Abrechen2/AirQualityMonitor/Pictures/IMG_7562.JPEG

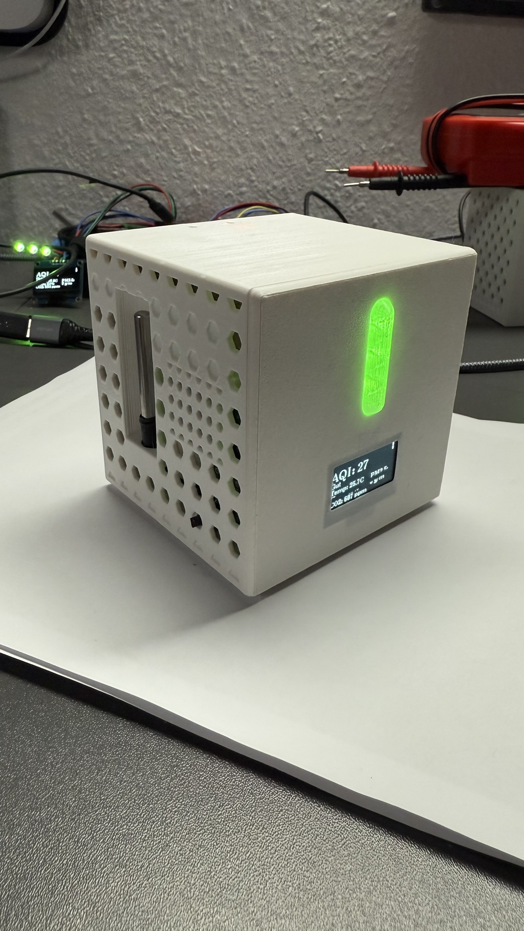
Pictures/IMG_7562.JPEG
