Abrechen2/AirQualityMonitor/Pictures/IMG_7563.JPEG

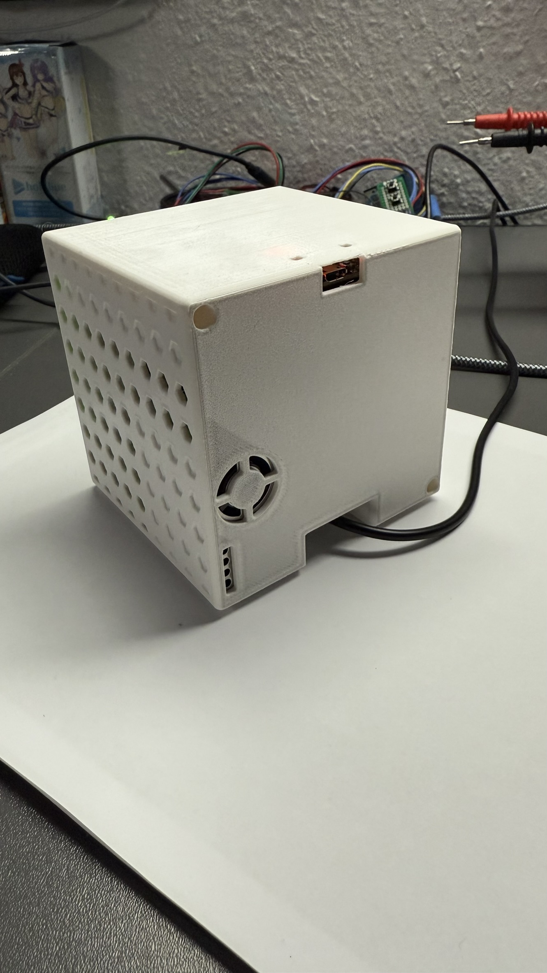
Pictures/IMG_7563.JPEG
