Abrechen2/AirQualityMonitor/Pictures/IMG_7564.JPEG

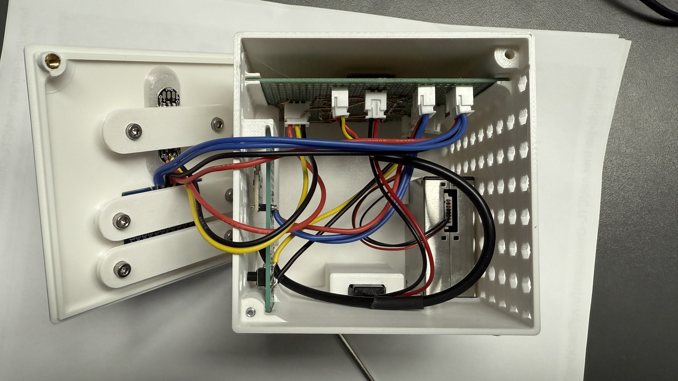
Pictures/IMG_7564.JPEG
