Abrechen2/AirQualityMonitor/Pictures/IMG_7565.JPEG

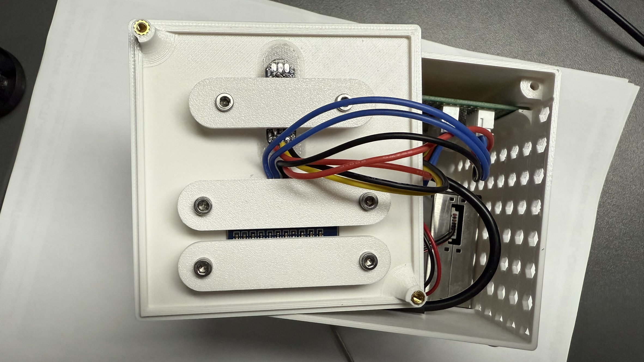
Pictures/IMG_7565.JPEG
