Abrechen2/AirQualityMonitor/Pictures/IMG_7566.JPEG

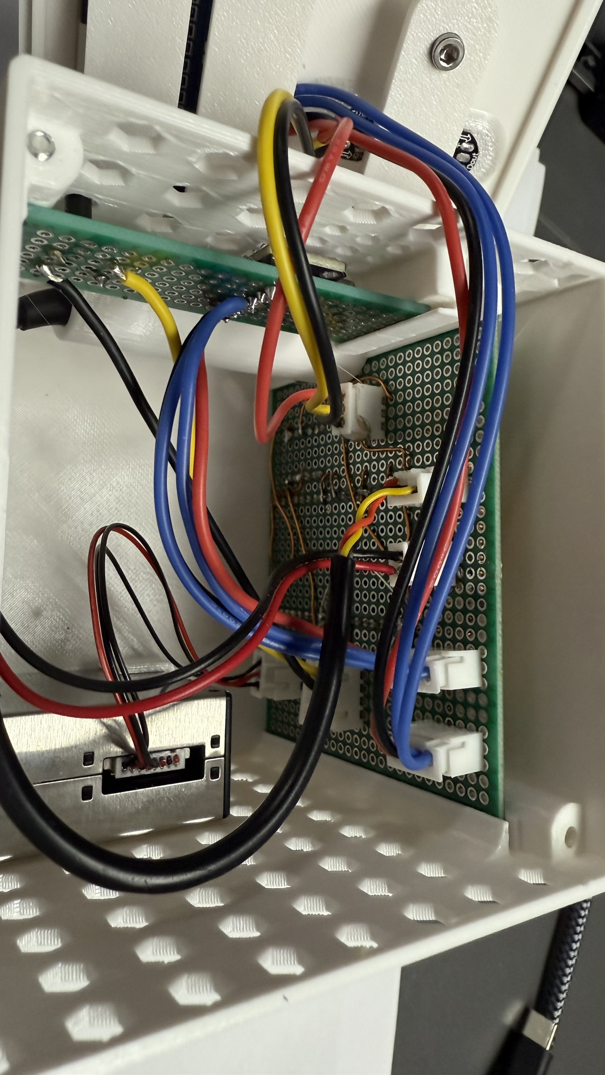
Pictures/IMG_7566.JPEG
