Abrechen2/AirQualityMonitor/Pictures/IMG_7568.JPEG

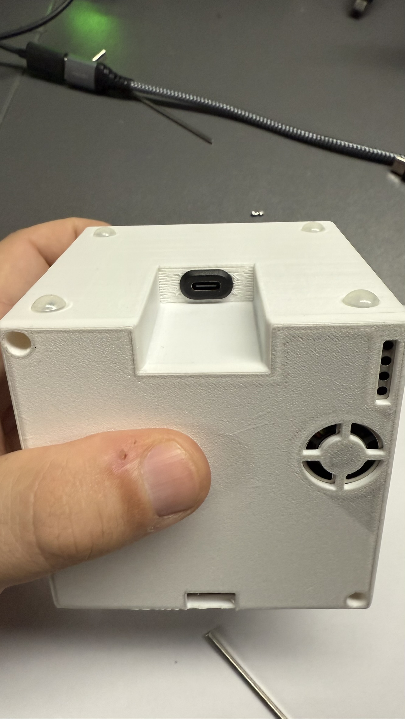
Pictures/IMG_7568.JPEG
