Abrechen2/AirQualityMonitor/Schematics/KiCad/AirQualityMonitor.kicad_sch

## KiCad design Schematics/KiCad/AirQualityMonitor.kicad_sch (2025-08-20, an earlier design)

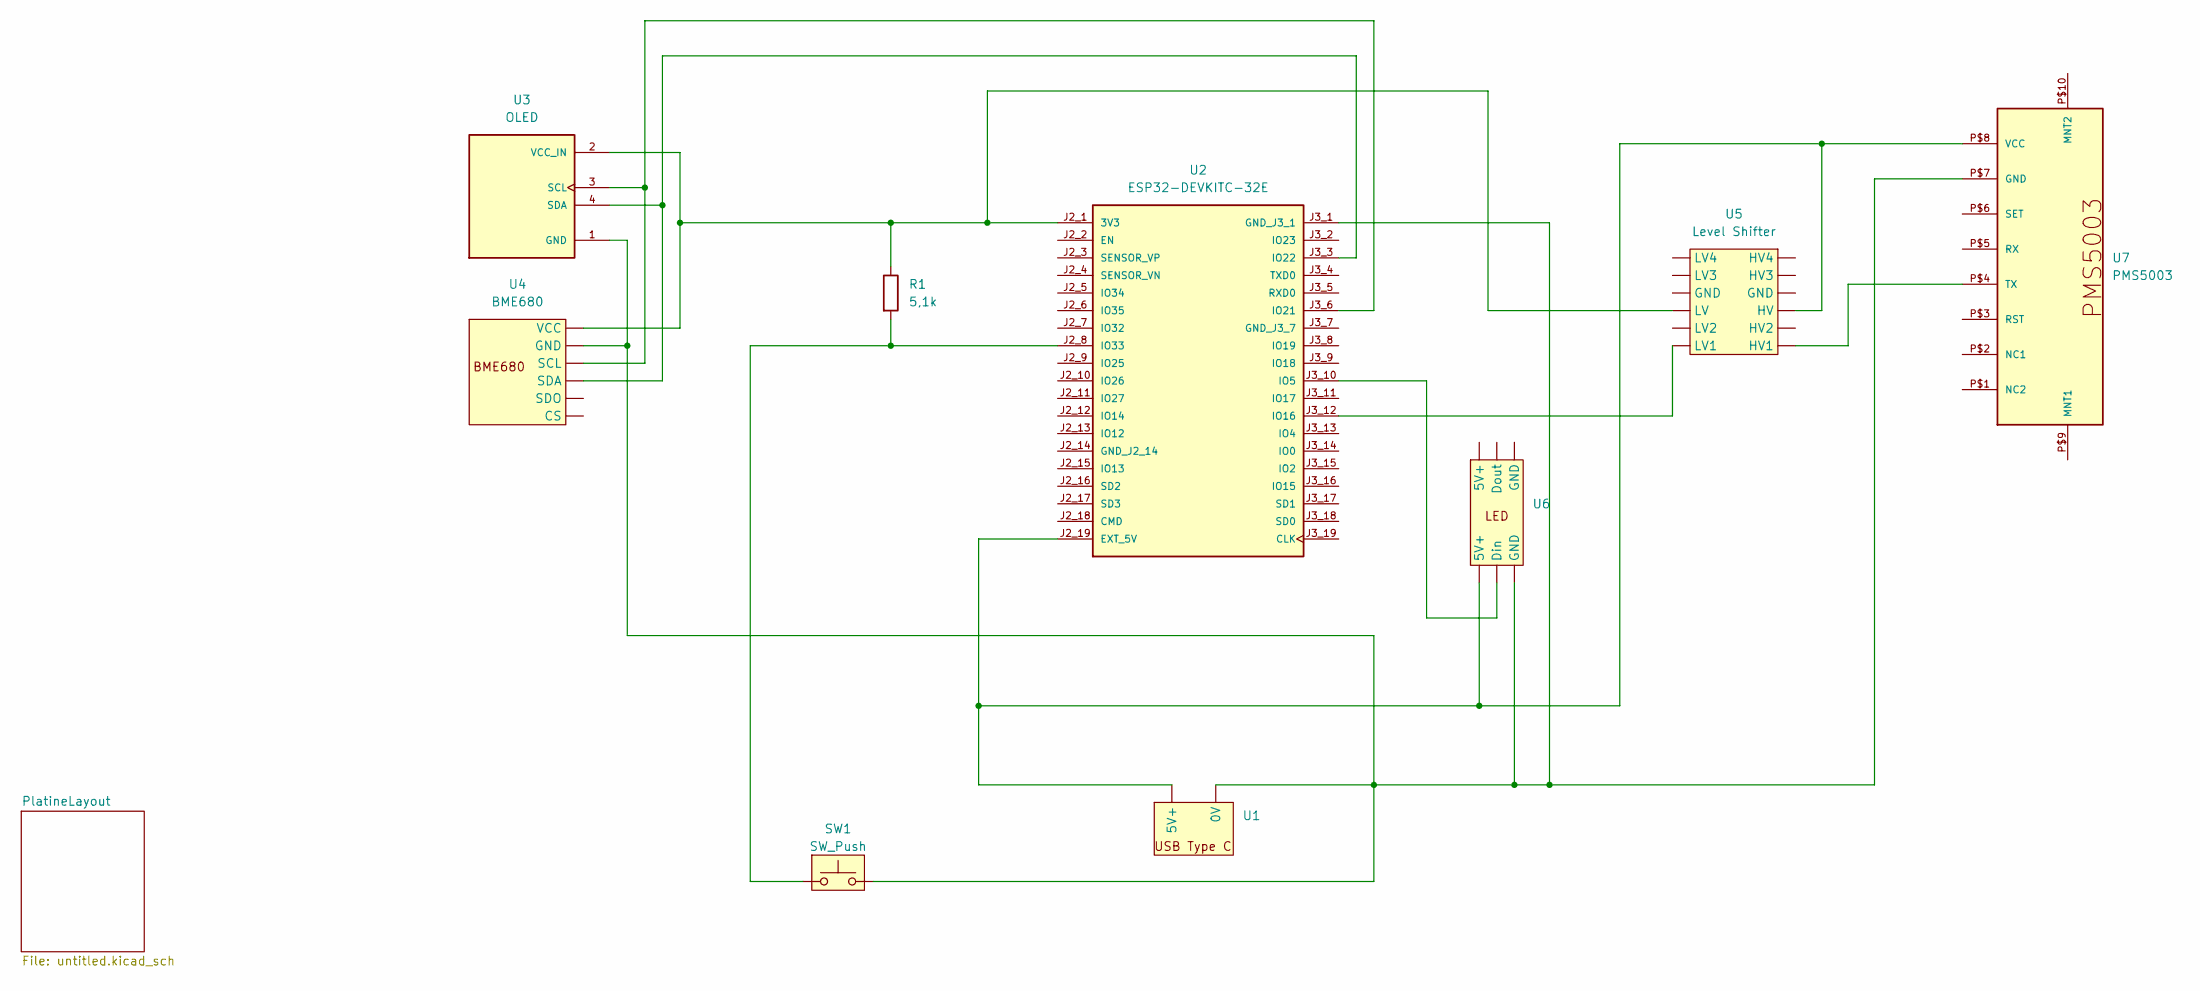
[picture p17: schematic AirQualityMonitor.kicad_sch]

Parts:
R1: 5,1k
SW1: SW_Push
U1, U6: (no value)
U2: ESP32-DEVKITC-32E; MODULE_ESP32-DEVKITC-32E; PARTREV 1.4
U3: OLED; MODULE_DM-OLED096-636; PARTREV 2018-09-10
U4: BME680
U5: Level Shifter
U7: PMS5003

Connections:
unnamed: R1.1, U2.J2_1 (3V3), U3.2 (VCC_IN), U4., U5.
unnamed: R1.2, SW1.1, U2.J2_8 (IO33)
unnamed: SW1.2, U1., U2.J3_1 (GND_J3_1), U3.1 (GND), U4., U6., U7.P$7 (GND)
unnamed: U1., U2.J2_19 (EXT_5V), U5., U6., U7.P$8 (VCC)
unnamed: U2.J3_3 (IO22), U3.4 (SDA), U4.
unnamed: U2.J3_6 (IO21), U3.3 (SCL), U4.
unnamed: U2.J3_10 (IO5), U6.
unnamed: U2.J3_12 (IO16), U5.
unnamed: U5., U7.P$4 (TX)
