Abrechen2/AirQualityMonitor/DisplayManager.h

#ifndef DISPLAY_MANAGER_H
#define DISPLAY_MANAGER_H

#include <Arduino.h>
#include <U8g2lib.h>
#include <Adafruit_NeoPixel.h>
#include <WiFi.h>
#include "config.h"
#include "SensorManager.h"
#include "TimeUtils.h"

// ===== DISPLAY MANAGER CLASS =====
class DisplayManager {
private:
  U8G2_SH1106_128X64_NONAME_F_HW_I2C& display;
  Adafruit_NeoPixel& leds;
  
  DisplayView currentView = VIEW_OVERVIEW;
  StealthMode stealthMode = STEALTH_OFF;
  bool displayEnabled = true;
  unsigned long stealthTempStartTime = 0;

  // Stealth countdown overlay state (driven by ButtonHandler during long press)
  bool countdownActive = false;
  int8_t lastDrawnCountdownSecond = -1;

  // Cache of last-drawn frame — lets us restore the normal view
  // immediately after the countdown overlay ends without waiting
  // for the next sensor update (~3s).
  SensorData lastSensorData{};
  float lastAqi = 0.0f;
  String lastAqiLevel = "";
  bool lastWifiConnected = false;
  bool hasLastFrame = false;

public:
  DisplayManager(U8G2_SH1106_128X64_NONAME_F_HW_I2C& disp, Adafruit_NeoPixel& strip);

  void init();
  void updateDisplay(const SensorData& data, float aqi, const String& aqiLevel,
                     bool wifiConnected);
  void showMessage(const String& message, int duration = 1000);

  // View control
  void nextView();
  void toggleStealth();
  void activateStealthTemp();

  // Stealth countdown overlay — called from ButtonHandler during long press
  void showStealthCountdown(uint16_t remainingMs);
  void hideStealthCountdown();
  bool isCountdownActive() const { return countdownActive; }

  // Status
  bool isDisplayEnabled() const { return displayEnabled; }
  DisplayView getCurrentView() const { return currentView; }
  StealthMode getStealthMode() const { return stealthMode; }

  void resetActivity() { /* no longer used */ }

private:
    void drawOverview(const SensorData& data, float aqi, const String& aqiLevel, bool wifiConnected);
    void drawEnvironment(const SensorData& data, bool wifiConnected);
    void drawParticles(const SensorData& data, float aqi, bool wifiConnected);
    void drawGas(const SensorData& data, bool wifiConnected);
    void drawSystem(const SensorData& data, bool wifiConnected);
    void drawWiFiIcon(int x, int y, bool connected);
    void drawConnectionBar(int x, int y, bool wifiConnected);
    String getShortLevelName(const String& level);
    // Helper for icon drawing - reduces duplication
    void drawStatusIcon(int x, int y, bool connected, bool isWiFi);
  void updateStealthMode();
  void updateDisplayBrightness();
  void drawStealthCountdownFrame(int seconds);
};

// ===== IMPLEMENTATION =====
DisplayManager::DisplayManager(U8G2_SH1106_128X64_NONAME_F_HW_I2C& disp, Adafruit_NeoPixel& strip) 
  : display(disp), leds(strip) {
}

void DisplayManager::init() {
  DEBUG_INFO("Initializing display...");
  
  // Check if display is available
  Wire.beginTransmission(0x3C);
  if (Wire.endTransmission() != 0) {
    DEBUG_WARN("Display not available");
    displayEnabled = false;
    return;
  }
  
  display.begin();
  display.clearBuffer();
  display.setFont(u8g2_font_ncenB08_tr);
  display.drawStr(10, 30, "Booting...");
  display.sendBuffer();
  
  updateDisplayBrightness();
  
  DEBUG_INFO("Display initialized successfully");
}

void DisplayManager::updateDisplay(const SensorData& data, float aqi, const String& aqiLevel, bool wifiConnected) {
  if (!displayEnabled) {
    return;
  }

  // Cache last frame data so hideStealthCountdown() can restore the view
  // immediately on button release (instead of waiting for the next sensor tick).
  lastSensorData = data;
  lastAqi = aqi;
  lastAqiLevel = aqiLevel;
  lastWifiConnected = wifiConnected;
  hasLastFrame = true;

  // While the stealth-countdown overlay is showing, the button handler owns
  // the screen — skip the normal redraw to avoid flicker.
  if (countdownActive) {
    return;
  }

  updateStealthMode();

  // In stealth mode: display off
  if (stealthMode == STEALTH_ON) {
    display.clearBuffer();
    display.sendBuffer();
    return;
  }

  display.clearBuffer();
  
    switch (currentView) {
      case VIEW_OVERVIEW:
        drawOverview(data, aqi, aqiLevel, wifiConnected);
        break;
      case VIEW_ENVIRONMENT:
        drawEnvironment(data, wifiConnected);
        break;
      case VIEW_PARTICLES:
        drawParticles(data, aqi, wifiConnected);
        break;
      case VIEW_GAS:
        drawGas(data, wifiConnected);
        break;
      case VIEW_SYSTEM:
        drawSystem(data, wifiConnected);
        break;
      default:
        break;
    }
  
  display.sendBuffer();
}

void DisplayManager::drawOverview(const SensorData& data, float aqi, const String& aqiLevel, bool wifiConnected) {
  // Status indicators
  display.setFont(u8g2_font_ncenB08_tr);
  drawConnectionBar(122, 0, wifiConnected);
  if (data.bsecCalibrated) {
    display.drawStr(112, 8, "*");
  }

  // AQI - large value
  display.setFont(u8g2_font_ncenB14_tr);
  display.setCursor(0, 24);
  if (aqi > 999) {
    display.setFont(u8g2_font_ncenB10_tr);
    display.printf("AQI:%.0f", aqi);
  } else {
    display.printf("AQI: %.0f", aqi);
  }

  // AQI Level
  display.setFont(u8g2_font_ncenB08_tr);
  display.setCursor(0, 34);
  String shortLevel = getShortLevelName(aqiLevel);
  display.print(shortLevel.c_str());

  // Main values - DS18B20 as primary temperature
  display.setFont(u8g2_font_ncenB08_tr);
  display.setCursor(0, 44);
  if (data.ds18b20Available) {
    display.printf("Temp: %.1f°C", data.externalTemp);  // DS18B20 as primary temperature
  } else if (data.bme68xAvailable) {
    display.printf("Temp: %.1f°C", data.temperature);   // BME680 fallback
  } else {
    display.print("Temp: N/A");
  }

  display.setCursor(0, 54);
  display.printf("Hum: %.0f%%", data.humidity);

  display.setCursor(0, 63);
  if (data.bme68xAvailable) {
    display.printf("CO2: %.0f ppm", data.co2Equivalent);
  } else {
    display.print("CO2: N/A");
  }

  // PM2.5 on the right
  display.setCursor(80, 44);
  display.printf("PM2.5:");
  display.setCursor(80, 54);
  display.printf("%d µg/m³", data.pm2_5);
}

void DisplayManager::drawEnvironment(const SensorData& data, bool wifiConnected) {
  display.setFont(u8g2_font_ncenB08_tr);
  display.drawStr(0, 10, "ENVIRONMENT");
  drawWiFiIcon(115, 10, wifiConnected);
  
  // DS18B20 as main temperature on top
  display.setCursor(0, 25);
  if (data.ds18b20Available) {
    display.printf("Main T: %.1f °C", data.externalTemp);
  } else {
    display.print("Main T: N/A");
  }
  
  // BME68X compensated values
  display.setCursor(0, 35);
  if (data.bme68xAvailable) {
    display.printf("BME T: %.1f °C", data.temperature);
    display.setCursor(0, 45);
    display.printf("Hum: %.1f %%", data.humidity);
    display.setCursor(0, 55);
    display.printf("Pres: %.0f hPa", data.pressure);
  } else {
    display.print("BME68X: N/A");
  }
  
  // Display temperature difference
  if (data.bme68xAvailable && data.ds18b20Available) {
    float tempDiff = data.externalTemp - data.temperature;
    display.setCursor(0, 62);
    display.printf("Diff: %+.1f °C", tempDiff);
  }
}

void DisplayManager::drawParticles(const SensorData& data, float aqi, bool wifiConnected) {
  display.setFont(u8g2_font_ncenB08_tr);
  display.drawStr(0, 10, "PARTICLES");
  drawWiFiIcon(115, 10, wifiConnected);
  
  if (data.pms5003Available) {
    display.setCursor(0, 25);
    display.printf("PM1.0: %d µg/m³", data.pm1_0);
    display.setCursor(0, 35);
    display.printf("PM2.5: %d µg/m³", data.pm2_5);
    display.setCursor(0, 45);
    display.printf("PM10:  %d µg/m³", data.pm10);
    
    display.setCursor(0, 60);
    display.printf("AQI: %.0f", aqi);
  } else {
    display.setCursor(0, 30);
    display.print("PMS5003: N/A");
  }
}

void DisplayManager::drawGas(const SensorData& data, bool wifiConnected) {
  display.setFont(u8g2_font_ncenB08_tr);
  display.drawStr(0, 10, "GAS SENSORS");
  drawWiFiIcon(115, 10, wifiConnected);

  if (data.bme68xAvailable) {
    // Calibration status
    display.setCursor(0, 22);
    display.printf("Cal: %s", data.bsecCalibrated ? "Yes" : "Learn");

    // CO2 equivalent with overflow check
    display.setCursor(0, 32);
    if (data.co2Equivalent > 9999) {
      display.print("CO2: >9999");
    } else {
      display.printf("CO2: %.0f ppm", data.co2Equivalent);
    }

    // VOC equivalent formatting
    display.setCursor(0, 42);
    if (data.breathVocEquivalent >= 10) {
      display.printf("VOC: %.0f mg/m³", data.breathVocEquivalent);
    } else {
      display.printf("VOC: %.1f mg/m³", data.breathVocEquivalent);
    }

    // IAQ values compact
    display.setCursor(0, 52);
    display.printf("IAQ:%.0f", data.iaq);

    display.setCursor(64, 52);
    display.printf("sIAQ:%.0f", data.staticIaq);

    // Gas resistance
    display.setCursor(0, 62);
    if (data.gasResistance >= 1000000) {
      display.printf("Gas: %.1fMΩ", data.gasResistance / 1000000.0);
    } else if (data.gasResistance >= 100000) {
      display.printf("Gas: %.0fkΩ", data.gasResistance / 1000.0);
    } else {
      display.printf("Gas: %.1fkΩ", data.gasResistance / 1000.0);
    }

  } else {
    display.setCursor(0, 30);
    display.print("BME68X: N/A");
  }
}

void DisplayManager::drawSystem(const SensorData& data, bool wifiConnected) {
  display.setFont(u8g2_font_ncenB08_tr);
  display.drawStr(0, 10, "SYSTEM");
  drawWiFiIcon(115, 10, wifiConnected);

  // Formatted uptime
  display.setCursor(0, 25);
  uint64_t uptimeSeconds = getUptimeMillis() / 1000;
  unsigned long days = uptimeSeconds / 86400;
  unsigned long hours = (uptimeSeconds % 86400) / 3600;
  unsigned long minutes = (uptimeSeconds % 3600) / 60;

  if (days > 99) {
    display.printf("Up: %lud", days);
  } else if (days > 0) {
    display.printf("Up: %lud %02luh", days, hours);
  } else if (hours > 0) {
    display.printf("Up: %luh %02lum", hours, minutes);
  } else {
    display.printf("Up: %lum", minutes);
  }
  
  // WiFi Status
  display.setCursor(0, 35);
  display.printf("WiFi: %s", wifiConnected ? "OK" : "Error");
  
  // IP-Adresse oder Offline
  display.setCursor(0, 45);
  if (wifiConnected) {
    display.print(WiFi.localIP().toString().c_str());
  } else {
    display.print("Offline");
  }

  // Sensor Count (left) + Firmware Version (right)
  display.setCursor(0, 62);
  display.printf("Sens: %d/3",
    (data.bme68xAvailable ? 1 : 0) + (data.ds18b20Available ? 1 : 0) + (data.pms5003Available ? 1 : 0));
  String ver = "v" + String(FIRMWARE_VERSION);
  int verWidth = display.getUTF8Width(ver.c_str());
  display.setCursor(SCREEN_WIDTH - verWidth, 62);
  display.print(ver.c_str());
}

void DisplayManager::drawWiFiIcon(int x, int y, bool connected) {
  if (connected) {
    // WiFi symbol - simple arcs
    display.drawPixel(x + 7, y);
    display.drawPixel(x + 6, y - 1);
    display.drawPixel(x + 8, y - 1);
    display.drawPixel(x + 5, y - 2);
    display.drawPixel(x + 9, y - 2);
    display.drawPixel(x + 4, y - 3);
    display.drawPixel(x + 10, y - 3);
  } else {
    // X for no connection
    display.drawStr(x, y, "X");
  }
}

void DisplayManager::drawConnectionBar(int x, int y, bool wifiConnected) {
  const uint8_t segmentWidth = 3;
  const uint8_t segmentHeight = 5;

  // Draw WiFi status segment
  if (wifiConnected) {
    display.drawBox(x, y, segmentWidth, segmentHeight);
  } else {
    display.drawFrame(x, y, segmentWidth, segmentHeight);
  }
}

String DisplayManager::getShortLevelName(const String& level) {
  if (level == "Unhealthy for sensitive groups") return "Unhlthy Sens";
  if (level == "Very unhealthy") return "Very Unhlthy";
  if (level == "Extremely unhealthy") return "Extr. Unhlthy";
  if (level == "Hazardous") return "Hazardous!";
  if (level.length() > 15) return level.substring(0, 14);
  return level;
}

void DisplayManager::showMessage(const String& message, int duration) {
  if (!displayEnabled) {
    DEBUG_WARN("Display not enabled - cannot show message");
    return;
  }
  
  if (message.length() == 0) {
    DEBUG_WARN("Empty message - skipping display");
    return;
  }
  
  display.clearBuffer();
  display.setFont(u8g2_font_ncenB08_tr);
  
  // Center text with bounds checking
  int textWidth = display.getUTF8Width(message.c_str());
  if (textWidth > SCREEN_WIDTH) {
    DEBUG_WARN("Message too wide: %d pixels (max: %d)", textWidth, SCREEN_WIDTH);
    // Truncate or use smaller font
    textWidth = SCREEN_WIDTH;
  }
  int x = (SCREEN_WIDTH - textWidth) / 2;
  if (x < 0) x = 0;
  
  display.drawStr(x, 32, message.c_str());
  
  // sendBuffer() returns void, so we can't check for errors
  display.sendBuffer();
  
  if (duration > 0) {
    delay(duration);
  }
}

void DisplayManager::nextView() {
  // View switching works in normal and temp mode
  if (stealthMode != STEALTH_ON) {
    int nextView = (int)currentView + 1;
    if (nextView >= VIEW_COUNT) {
      nextView = 0;
    }
    currentView = (DisplayView)nextView;
    DEBUG_INFO("Display view changed to: %d", currentView);
  } else {
    // In full stealth mode: activate temporarily
    activateStealthTemp();
  }
}

void DisplayManager::toggleStealth() {
  if (stealthMode == STEALTH_OFF) {
    stealthMode = STEALTH_ON;
    DEBUG_INFO("Stealth mode ON - display and LEDs dimmed");
  } else {
    stealthMode = STEALTH_OFF;
    DEBUG_INFO("Stealth mode OFF - display and LEDs normal");
  }
  updateDisplayBrightness();
}

void DisplayManager::activateStealthTemp() {
  if (stealthMode == STEALTH_ON) {
    stealthMode = STEALTH_TEMP_ON;
    stealthTempStartTime = millis();
    updateDisplayBrightness();
    DEBUG_INFO("Stealth temporarily activated for 20s");
  }
}

void DisplayManager::updateStealthMode() {
  // Temporary stealth mode timeout
  if (stealthMode == STEALTH_TEMP_ON) {
    if (millis() - stealthTempStartTime > STEALTH_TEMP_ON_MS) {
      stealthMode = STEALTH_ON;
      updateDisplayBrightness();
      DEBUG_INFO("Stealth temporary mode ended - back to stealth");
    }
  }
}

void DisplayManager::updateDisplayBrightness() {
  if (!displayEnabled) return;

  if (stealthMode == STEALTH_ON) {
    display.setContrast(DISPLAY_CONTRAST_STEALTH); // Display off
  } else {
    display.setContrast(DISPLAY_CONTRAST_NORMAL);  // Display normal
  }
}

// ===== STEALTH COUNTDOWN OVERLAY =====
// Called repeatedly from ButtonHandler while the select button is held.
// Ceiling-rounds remainingMs to whole seconds so the shown digit ticks
// 3 -> 2 -> 1 cleanly. Internally rate-limited: only redraws when the
// shown digit changes, so a fast main loop doesn't thrash the OLED.
void DisplayManager::showStealthCountdown(uint16_t remainingMs) {
  if (!displayEnabled) return;

  // Temporarily bring the display to full contrast so the countdown
  // is visible even when stealth mode was active beforehand.
  if (!countdownActive) {
    display.setContrast(DISPLAY_CONTRAST_NORMAL);
  }

  countdownActive = true;

  // Ceiling division: 3000 -> 3, 2001 -> 3, 2000 -> 2, 1 -> 1, 0 -> 0
  int seconds = (int)((remainingMs + 999) / 1000);
  if (seconds < 0) seconds = 0;
  if (seconds > 9) seconds = 9;

  if (seconds == lastDrawnCountdownSecond) {
    return;  // Nothing changed -> avoid redraw
  }

  drawStealthCountdownFrame(seconds);
  lastDrawnCountdownSecond = seconds;
}

void DisplayManager::drawStealthCountdownFrame(int seconds) {
  display.clearBuffer();

  // Header
  display.setFont(u8g2_font_ncenB08_tr);
  const char* header = "STEALTH MODE";
  int headerW = display.getUTF8Width(header);
  display.drawStr((SCREEN_WIDTH - headerW) / 2, 10, header);

  // Big countdown digit — logisoso32 is numeric-only and exactly
  // what we need here (32px tall, clean sans).
  display.setFont(u8g2_font_logisoso32_tn);
  char digit[2] = { (char)('0' + seconds), '\0' };
  int digitW = display.getUTF8Width(digit);
  display.drawStr((SCREEN_WIDTH - digitW) / 2, 48, digit);

  // Footer hint
  display.setFont(u8g2_font_ncenB08_tr);
  const char* hint = "Halten...";
  int hintW = display.getUTF8Width(hint);
  display.drawStr((SCREEN_WIDTH - hintW) / 2, 62, hint);

  display.sendBuffer();
}

void DisplayManager::hideStealthCountdown() {
  if (!countdownActive) return;

  countdownActive = false;
  lastDrawnCountdownSecond = -1;

  // Restore the brightness appropriate for the current stealth mode.
  updateDisplayBrightness();

  // Immediately redraw the normal view with cached sensor data so the
  // countdown doesn't linger on screen until the next sensor update.
  if (hasLastFrame) {
    updateDisplay(lastSensorData, lastAqi, lastAqiLevel, lastWifiConnected);
  } else {
    display.clearBuffer();
    display.sendBuffer();
  }
}

#endif
